dlford/quokka/3D Case/src/3d_case_base.dxf

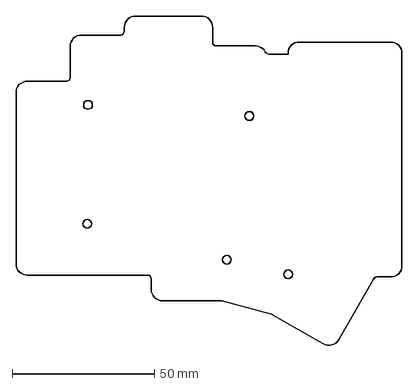
[picture p36: CAD file, 2023-05-05]
3D Case/src/3d_case_base.dxf
135.5 x 116.2 mm
