dlford/quokka/3D Case/src/3d_case_spacer.dxf

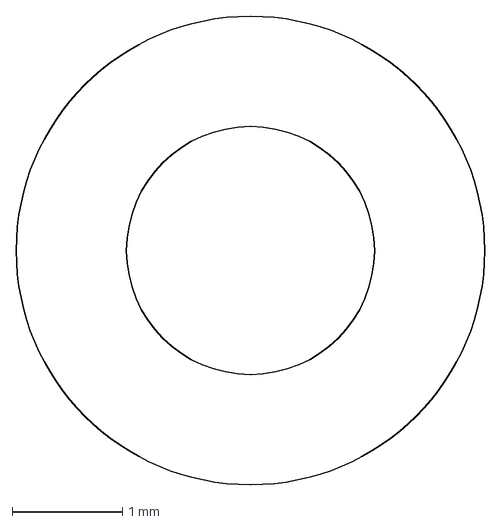
[picture p37: CAD file, 2023-04-18]
3D Case/src/3d_case_spacer.dxf
4.25 x 4.25 mm
