dlford/quokka/3D Case/src/3d_case_pcb_risers.dxf

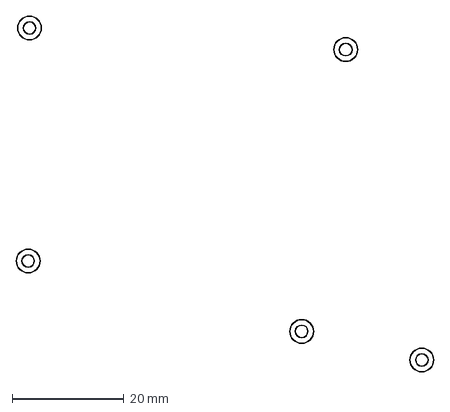
[picture p38: CAD file, 2023-04-18]
3D Case/src/3d_case_pcb_risers.dxf
74.8 x 63.7 mm
