dlford/quokka/3D Case/src/3d_case_switch_cutouts_wide.dxf

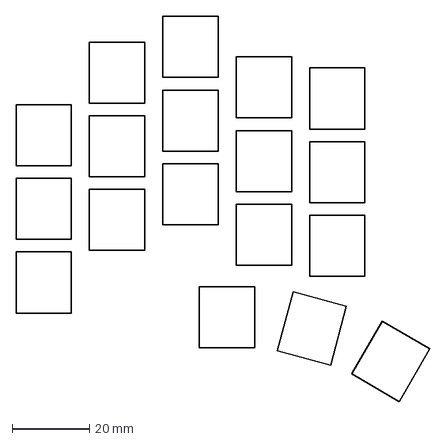
[picture p39: CAD file, 2023-04-18]
3D Case/src/3d_case_switch_cutouts_wide.dxf
107.1 x 99.7 mm
