dlford/quokka/3D Case/src/3d_case_switch_cutouts.dxf

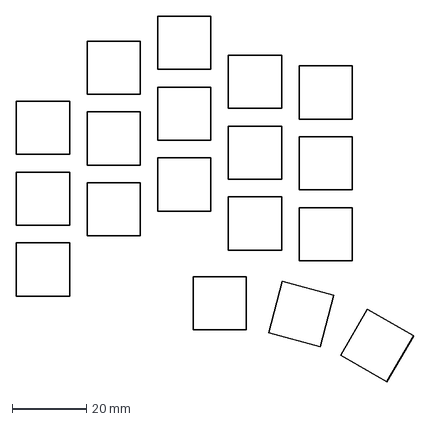
[picture p40: CAD file, 2023-04-18]
3D Case/src/3d_case_switch_cutouts.dxf
106.8 x 98.3 mm
