dlford/quokka/3D Case/src/3d_case_base_upper.dxf

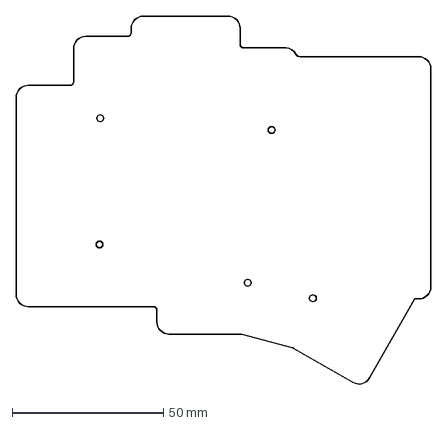
[picture p41: CAD file, 2023-04-18]
3D Case/src/3d_case_base_upper.dxf
137.0 x 122.1 mm
