dlford/quokka/3D Case/src/3d_case_keycaps.dxf

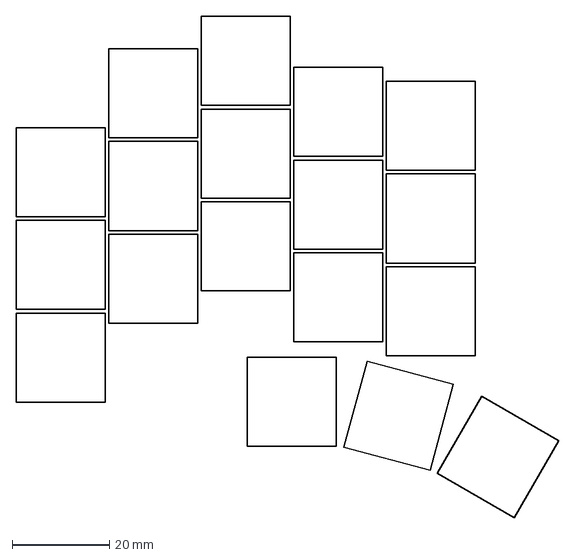
[picture p42: CAD file, 2023-04-18]
3D Case/src/3d_case_keycaps.dxf
111.5 x 103.0 mm
