dlford/quokka/img/build/22.jpg

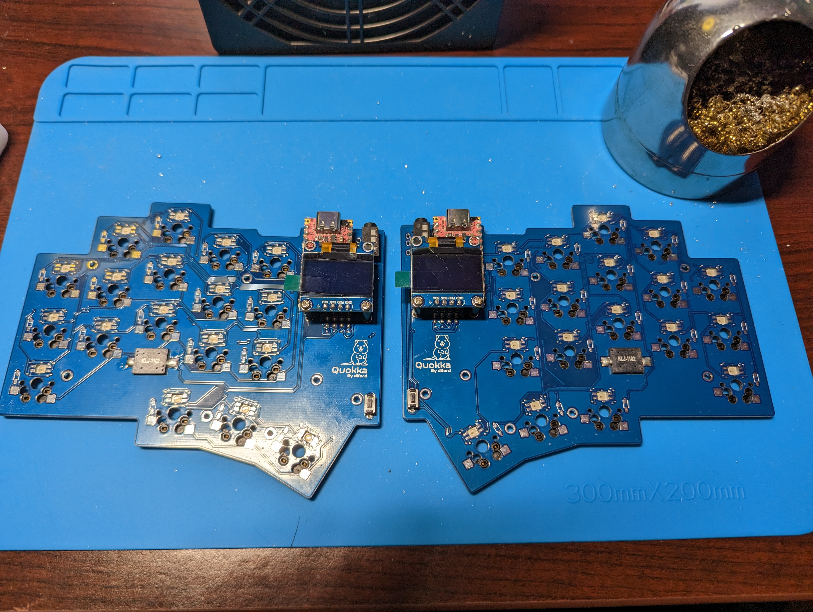
img/build/22.jpg
